terencelaniyan/smart-parking-occupancy/Hardware/Smart parking project .kicad_sch

## KiCad design Hardware/Smart parking project .kicad_sch (2026-05-22)

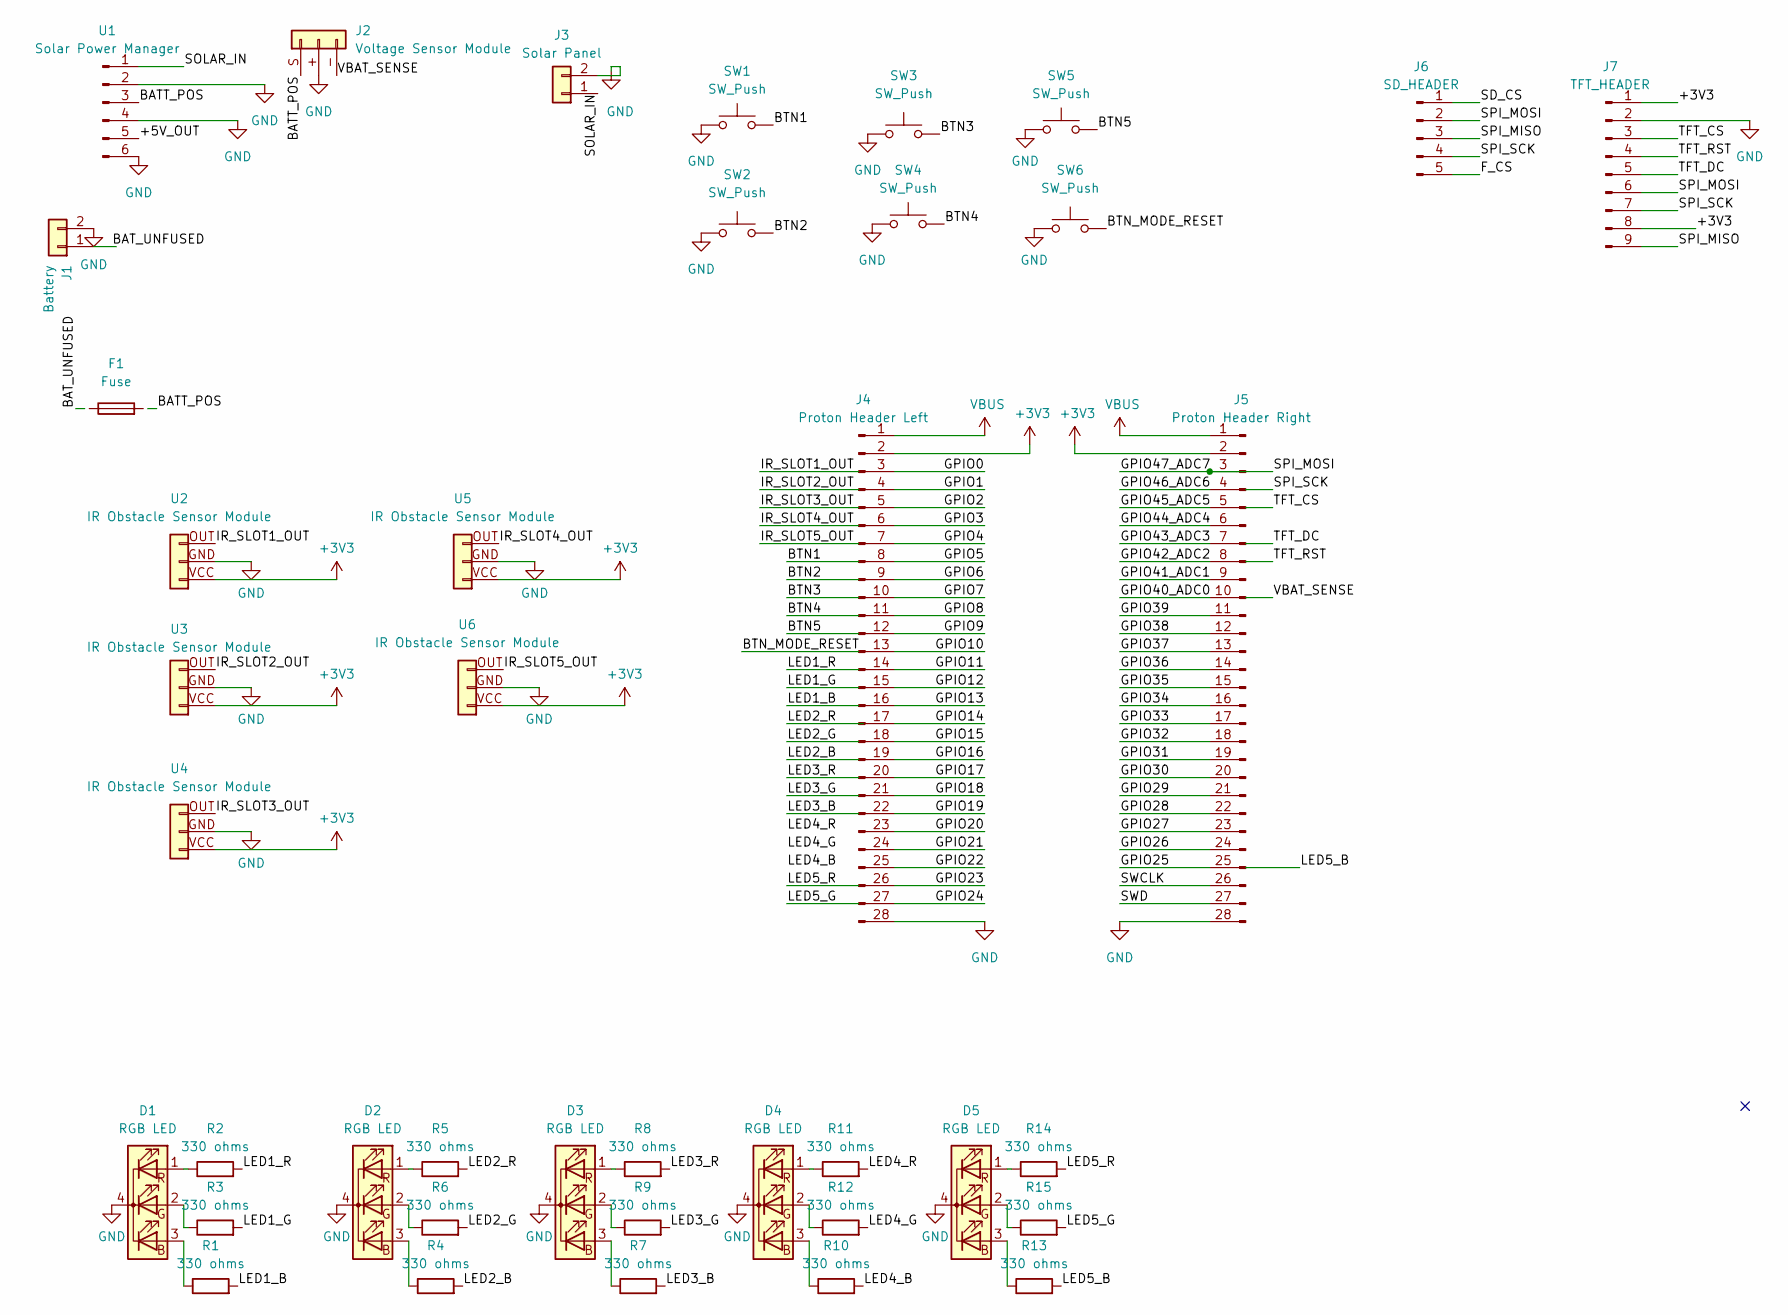
[picture p15: schematic Smart parking project .kicad_sch]

Parts:
D1, D2, D3, D4, D5: RGB LED
F1: Fuse
J1: Battery
J2: Voltage Sensor Module
J3: Solar Panel
J4: Proton Header Left; PinHeader_1x28_P2.54mm_Vertical
J5: Proton Header Right; PinHeader_1x28_P2.54mm_Vertical
J6: SD_HEADER
J7: TFT_HEADER
R1, R2, R3, R4, R5, R6, R7, R8, R9, R10, R11, R12, R13, R14, R15: 330 ohms
SW1, SW2, SW3, SW4, SW5, SW6: SW_Push
U1: Solar Power Manager
U2, U3, U4, U5, U6: IR Obstacle Sensor Module

Connections:
+3V3: J4.2, J5.2, J7.1, J7.8, U2.VCC (Pin_1), U3.VCC (Pin_1), U4.VCC (Pin_1), U5.VCC (Pin_1), U6.VCC (Pin_1)
+5V_OUT: U1.5
BATT_POS: J2.S (Pin_1), U1.3
BAT_UNFUSED: J1.1
BTN1: SW1.2
BTN2: SW2.2
BTN3: SW3.2
BTN4: SW4.2
BTN5: SW5.2
BTN_MODE_RESET: SW6.2
F_CS: J6.5
GND: D1.4 (K), D2.4 (K), D3.4 (K), D4.4 (K), D5.4 (K), J1.2, J2.+ (Pin_2), J3.2, J4.28, J5.28, J7.2, SW1.1, SW2.1, SW3.1, SW4.1, SW5.1, SW6.1, U1.2, U1.4, U1.6, U2.GND (Pin_2), U3.GND (Pin_2), U4.GND (Pin_2), U5.GND (Pin_2), U6.GND (Pin_2)
GPIO0: J4.3
GPIO1: J4.4
GPIO2: J4.5
GPIO3: J4.6
GPIO4: J4.7
GPIO5: J4.8
GPIO6: J4.9
GPIO7: J4.10
GPIO8: J4.11
GPIO9: J4.12
GPIO10: J4.13
GPIO11: J4.14
GPIO12: J4.15
GPIO13: J4.16
GPIO14: J4.17
GPIO15: J4.18
GPIO16: J4.19
GPIO17: J4.20
GPIO18: J4.21
GPIO19: J4.22
GPIO20: J4.23
GPIO21: J4.24
GPIO22: J4.25
GPIO23: J4.26
GPIO24: J4.27
GPIO25: J5.25
GPIO26: J5.24
GPIO27: J5.23
GPIO28: J5.22
GPIO29: J5.21
GPIO30: J5.20
GPIO31: J5.19
GPIO32: J5.18
GPIO33: J5.17
GPIO34: J5.16
GPIO35: J5.15
GPIO36: J5.14
GPIO37: J5.13
GPIO38: J5.12
GPIO39: J5.11
GPIO40_ADC0: J5.10
GPIO41_ADC1: J5.9
GPIO42_ADC2: J5.8
GPIO43_ADC3: J5.7
GPIO44_ADC4: J5.6
GPIO45_ADC5: J5.5
GPIO46_ADC6: J5.4
GPIO47_ADC7: J5.3, J6.2, J7.6
IR_SLOT1_OUT: U2.OUT (Pin_3)
IR_SLOT2_OUT: U3.OUT (Pin_3)
IR_SLOT3_OUT: U4.OUT (Pin_3)
IR_SLOT4_OUT: U5.OUT (Pin_3)
IR_SLOT5_OUT: U6.OUT (Pin_3)
LED1_B: R1.2
LED1_G: R3.2
LED1_R: R2.2
LED2_B: R4.2
LED2_G: R6.2
LED2_R: R5.2
LED3_B: R7.2
LED3_G: R9.2
LED3_R: R8.2
LED4_B: R10.2
LED4_G: R12.2
LED4_R: R11.2
LED5_B: R13.2
LED5_G: R15.2
LED5_R: R14.2
unnamed: D1.1 (RA), R2.1
unnamed: D1.2 (GA), R3.1
unnamed: D1.3 (BA), R1.1
unnamed: D2.1 (RA), R5.1
unnamed: D2.2 (GA), R6.1
unnamed: D2.3 (BA), R4.1
unnamed: D3.1 (RA), R8.1
unnamed: D3.2 (GA), R9.1
unnamed: D3.3 (BA), R7.1
unnamed: D4.1 (RA), R11.1
unnamed: D4.2 (GA), R12.1
unnamed: D4.3 (BA), R10.1
unnamed: D5.1 (RA), R14.1
unnamed: D5.2 (GA), R15.1
unnamed: D5.3 (BA), R13.1
SD_CS: J6.1
SOLAR_IN: J3.1, U1.1
SPI_MISO: J6.3, J7.9
SPI_SCK: J6.4, J7.7
SWCLK: J5.26
SWD: J5.27
TFT_CS: J7.3
TFT_DC: J7.5
TFT_RST: J7.4
VBAT_SENSE: J2.- (Pin_3)
VBUS: J4.1, J5.1
